TDA-2030/E-ink-screen/firmware/spiffs_image/5.jpg

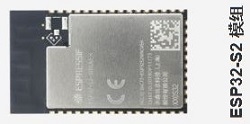
firmware/spiffs_image/5.jpg
