TDA-2030/E-ink-screen/firmware/spiffs_image/12.jpg

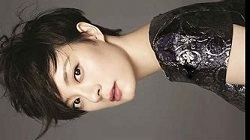
firmware/spiffs_image/12.jpg
