TDA-2030/E-ink-screen/firmware/components/file_server/include/file_manage.h

#ifndef FILE_MANAGE_H_
#define FILE_MANAGE_H_

#ifdef __cplusplus 
extern "C" {
#endif

#include "esp_log.h"



typedef struct {
    char *base_path;
    char *label;

} fs_info_t;


esp_err_t fm_init(void);

esp_err_t fm_get_info(fs_info_t **info);

esp_err_t fm_file_table_create(char ***list_out, uint16_t *files_number);
esp_err_t fm_file_table_free(char ***list,uint16_t files_number);


#ifdef __cplusplus 
}
#endif

#endif
